theovidal/mapping/assets/tests/EC 25.05.21/test 2 épuré.txt

0 0 178
0 3.49 199.969
0 6.456 184.887
0 9.158 174.76
0 11.788 168.588
0 14.032 160.387
0 16.306 155.145
0 18.28 148.881
0 19.762 140.618
0 22.37 141.239
0 24.31 137.873
0 26.713 137.427
0 28.483 134.006
0 30.818 133.488
0 33.627 134.871
0 35.975 134.263
0 38.589 134.576
0 44.148 144.402
0 46.97 144.56
0 49.811 144.664
0 53.013 145.652
0 55.547 144.704
0 58.438 144.64
0 60.954 143.598
0 64.264 144.34
0 66.773 143.196
0 70.577 144.705
0 73.546 144.343
0 76.993 144.803
0 80.963 146.061
0 84 145.492
0 88.071 146.575
0 91.676 146.712
0 95.311 146.767
0 98.977 146.739
0 102.67 146.628
0 106.389 146.432
0 110.132 146.15
0 114.513 146.569
0 118.941 146.88
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
