theovidal/mapping/assets/tests/EC 25.05.21/test 3.txt

0 421.581 -89.61
0 720.292 -3119.932
0 631.011 -2968.677
0 408.712 -2102.645
0 369.349 -2094.686
0 330.702 -2087.973
0 291.706 -2075.601
0 254.219 -2070.451
0 216.268 -2057.665
0 178.669 -2042.199
0 142.86 -2043.011
0 62.593 -1194.36
0 49.976 -1431.127
0 25.655 -1469.776
0 0 -1488
2.827 0 161.975
2.809 2.809 160.95
2.79 5.583 159.878
3.1189999999999998 9.368 178.727
2.89 11.579 165.57
2.799 14.032 160.362
2.6550000000000002 15.992 152.138
2.632 18.524 150.844
2.609 21.015 149.507
2.62 23.778 150.105
2.629 26.568 150.652
2.586 28.812 148.203
2.594 31.602 148.655
2.584 34.192 148.081
2.573 36.772 147.462
2.5789999999999997 39.599 147.764
2.583 42.448 148.011
2.586 45.317 148.204
2.589 48.206 148.342
2.59 51.114 148.423
2.591 54.039 148.448
2.59 56.98 148.416
2.589 59.937 148.326
2.586 62.907 148.178
2.598 66.298 148.885
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
