theovidal/mapping/assets/tests/SC 18.05.21/test3.txt

0 0 190
0 3.665 209.968
0 7.189 205.874
0 12.822 244.664
0 17.439 249.391
0 21.614 247.056
0 25.923000000000002 246.641
0 29.979 244.166
0 34.097 242.615
0 34.884 220.254
0 34.729 196.961
0 35.872 184.545
0 39.295 184.869
0 42.515 184.155
0 45.481 182.415
0 48.657 181.594
0 52.095 181.678
0 55.258 180.741
0 58.404 179.749
0 61.532 178.703
0 64.299 176.662
0 67.014 174.579
0 70.426 174.31
0 74.238 174.895
0 78.093 175.4
0 81.142 174.011
0 83.728 171.669
0 63.558 124.74
0 78.401 147.452
0 96.961 174.923
0 101.5 175.803
0 105.582 175.719
0 109.693 175.545
0 113.829 175.282
0 117.989 174.926
0 123.318 176.117
0 128.137 176.365
0 132.399 175.699
0 137.292 175.726
0 142.226 175.634
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
