theovidal/mapping/assets/tests/SC 18.05.21/test 2.txt

0 0 304
0 5.6370000000000005 322.95
0 11.202 320.804
0 17.323 330.546
0 24.065 344.159
0 31.811 363.611
0 27.386 260.564
0 29.736 242.181
0 31.453 223.8
0 33.633 212.352
0 35.424 200.9
0 37.207 191.417
0 38.671 181.935
0 42.965 186.104
0 44.997 180.474
0 47.881 178.696
0 51.819 180.717
0 54.965 179.785
0 58.713 180.7
0 62.509 181.539
0 66.351 182.3
0 70.24 182.981
0 73.797 182.655
0 78.146 184.1
0 81.347 182.709
0 85.368 183.074
0 90.304 185.151
0 71.276 139.888
0 96.241 181.004
0 103.264 186.294
0 107 185.329
0 111.248 185.148
0 116.052 185.722
0 119.82 184.507
0 124.14 184.046
0 128.481 183.49
0 134.015 184.455
0 139.621 185.283
0 144.064 184.394
0 149.778 184.96
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
